rorosaurus/gba-sp-usb-c/references/usb-c.png

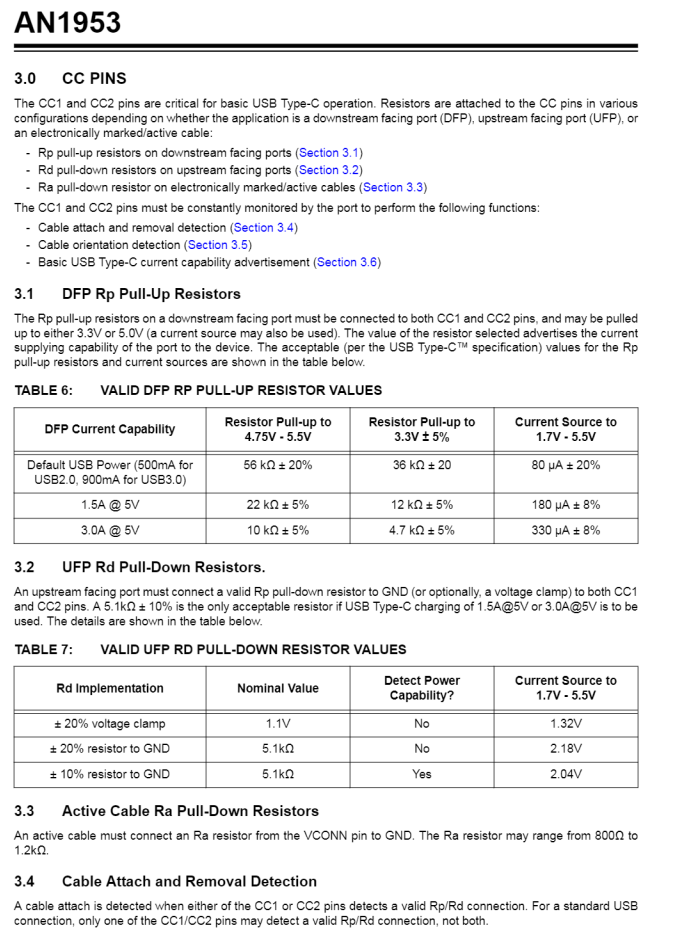
references/usb-c.png
