rorosaurus/gba-sp-usb-c/images/assembled-comparison.png

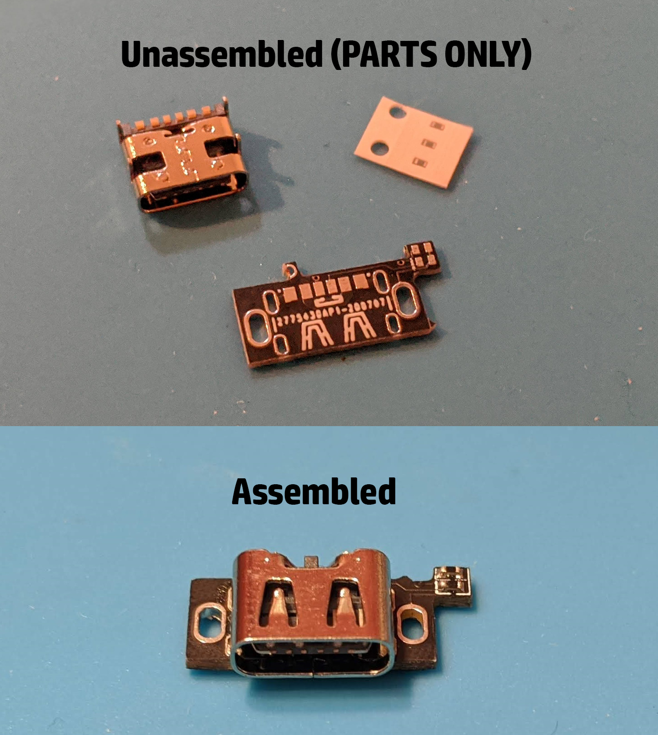
images/assembled-comparison.png
